TheItroma/Stradex1/3DFiles/OriginalFiles/KEY(4).3mf

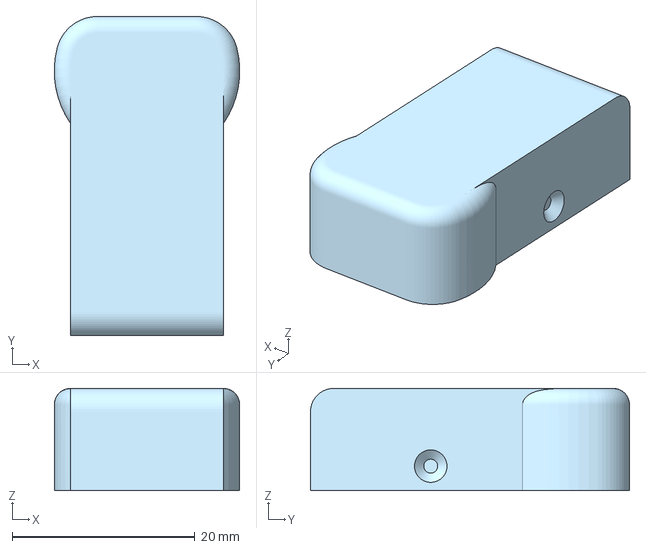
[picture p5: CAD file, 2025-09-11]
3DFiles/OriginalFiles/KEY(4).3mf
20.3 x 34.9 x 11.2 mm
